wez/SpockKeyboard/Spockduino/Keyboard.cpp

/*
  Keyboard.cpp

  Copyright (c) 2015, Arduino LLC
  Original code (pre-library): Copyright (c) 2011, Peter Barrett

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
  You should have received a copy of the GNU Lesser General Public
  License along with this library; if not, write to the Free Software
  Foundation, Inc., 51 Franklin St, Fifth Floor, Boston, MA  02110-1301  USA
*/

#include "Keyboard.h"

//================================================================================
//================================================================================
//	Keyboard

static const uint8_t _hidReportDescriptor[] PROGMEM = {

  //  Keyboard
    0x05, 0x01,                    // USAGE_PAGE (Generic Desktop)  // 47
    0x09, 0x06,                    // USAGE (Keyboard)
    0xa1, 0x01,                    // COLLECTION (Application)
    0x85, 0x02,                    //   REPORT_ID (2)
    0x05, 0x07,                    //   USAGE_PAGE (Keyboard)

  0x19, 0xe0,                    //   USAGE_MINIMUM (Keyboard LeftControl)
    0x29, 0xe7,                    //   USAGE_MAXIMUM (Keyboard Right GUI)
    0x15, 0x00,                    //   LOGICAL_MINIMUM (0)
    0x25, 0x01,                    //   LOGICAL_MAXIMUM (1)
    0x75, 0x01,                    //   REPORT_SIZE (1)

  0x95, 0x08,                    //   REPORT_COUNT (8)
    0x81, 0x02,                    //   INPUT (Data,Var,Abs)
    0x95, 0x01,                    //   REPORT_COUNT (1)
    0x75, 0x08,                    //   REPORT_SIZE (8)
    0x81, 0x03,                    //   INPUT (Cnst,Var,Abs)

  0x95, 0x06,                    //   REPORT_COUNT (6)
    0x75, 0x08,                    //   REPORT_SIZE (8)
    0x15, 0x00,                    //   LOGICAL_MINIMUM (0)
    0x25, 0xff,                    //   LOGICAL_MAXIMUM (255)
    0x05, 0x07,                    //   USAGE_PAGE (Keyboard)

  0x19, 0x00,                    //   USAGE_MINIMUM (Reserved (no event indicated))
    0x29, 0xff,                    //   USAGE_MAXIMUM (255)
    0x81, 0x00,                    //   INPUT (Data,Ary,Abs)
    0xc0,                          // END_COLLECTION
};

Keyboard_::Keyboard_(void)
{
	static HIDSubDescriptor node(_hidReportDescriptor, sizeof(_hidReportDescriptor));
	HID().AppendDescriptor(&node);
}

void Keyboard_::begin(void)
{
}

void Keyboard_::end(void)
{
}

void Keyboard_::sendReport(KeyReport* keys)
{
	HID().SendReport(2,keys,sizeof(KeyReport));
}

void Keyboard_::releaseAll(void)
{
  KeyReport report;
  memset(&report, 0, sizeof(report));
	sendReport(&report);
}

Keyboard_ Keyboard;
